lsr1/wb2s-to-esp12/ESPhome/cellphone-screenshot.png

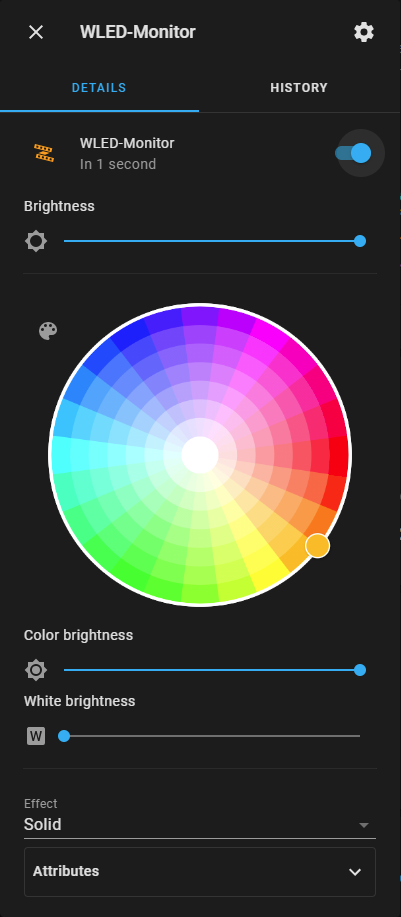
ESPhome/cellphone-screenshot.png
